tpwrules/emdash/dashboard/src_gen/pic_data.c

#include <inttypes.h>
#include "../src/pic_data.h"

static const uint8_t pic_bytes[3980] = {
113,7,60,72,201,7,27,214,48,31,32,7,56,201,3,27,8,195,1,54,
66,136,194,4,146,195,25,62,3,63,56,201,3,27,24,195,1,2,12,55,
12,38,115,1,38,12,3,8,39,21,35,12,83,56,31,60,24,201,3,25,
24,195,1,50,21,2,17,21,9,6,117,20,6,21,50,28,52,20,79,35,
63,197,15,63,63,194,3,9,24,195,1,2,25,2,17,21,9,3,1,21,
20,3,20,34,29,20,24,94,15,56,195,1,63,63,63,63,63,60,65,45,
40,195,1,55,12,51,16,37,8,54,1,53,12,6,8,35,29,52,12,1,
56,31,32,7,48,191,63,63,63,63,63,63,56,1,45,40,212,3,33,62,
3,63,48,71,48,67,63,63,63,63,63,33,45,40,196,1,129,65,32,65,
80,1,4,132,15,3,56,31,61,48,94,3,63,48,63,63,60,1,63,57,
37,40,196,2,8,48,21,35,12,32,25,35,118,13,38,9,35,12,12,15,
3,63,32,65,56,63,63,62,15,63,51,60,125,36,32,196,7,21,93,21,
20,32,13,21,1,19,25,21,20,52,20,124,15,60,131,33,63,63,63,47,
63,15,63,60,14,52,32,196,2,21,93,22,24,32,21,21,1,21,13,21,
21,20,20,1,48,63,48,31,63,63,9,63,63,63,47,63,31,63,60,55,
54,48,196,2,9,93,19,13,48,29,19,119,25,22,9,52,12,7,3,62,
3,63,63,62,29,63,63,63,47,62,31,63,60,59,54,48,213,15,56,31,
56,63,60,61,63,63,63,47,62,63,63,60,61,54,48,197,4,52,1,35,
9,48,29,194,1,16,8,194,63,3,63,127,61,61,63,63,63,47,62,63,
63,60,61,54,48,197,9,2,85,25,16,9,34,29,35,1,22,28,50,24,
3,56,31,56,127,57,61,63,63,63,47,62,63,63,60,62,54,16,197,9,
2,101,9,48,9,21,28,54,1,51,9,37,20,31,1,63,71,63,59,61,
63,63,63,47,62,63,63,60,62,62,24,197,9,2,1,5,9,16,9,21,
29,19,1,53,8,53,20,24,15,56,1,63,63,51,61,63,63,63,15,62,
31,63,60,62,59,24,197,4,52,1,54,9,48,9,18,21,54,1,23,13,
34,20,1,62,95,49,63,55,60,63,63,63,31,63,31,63,60,62,59,24,
212,15,32,7,62,1,63,39,60,63,63,63,31,63,31,63,60,62,59,24,
195,8,36,1,194,4,32,152,68,68,80,56,1,63,65,63,39,60,63,63,
63,31,63,31,63,60,62,59,195,3,1,54,21,32,12,39,5,54,20,53,
8,51,4,55,13,35,24,95,48,71,63,39,60,63,63,63,31,63,47,63,
60,62,63,195,5,8,37,21,16,17,23,8,37,29,5,9,22,9,23,20,
54,20,3,60,67,63,63,39,60,63,63,62,63,63,47,63,60,62,63,195,
7,8,37,21,16,17,23,16,37,29,5,9,35,17,39,21,19,20,6,191,
49,63,39,62,63,63,62,62,15,47,63,60,62,63,195,1,8,53,13,34,
12,37,16,54,29,3,28,54,16,53,13,54,20,191,60,1,63,39,62,63,
63,62,60,15,55,63,60,62,63,195,2,198,4,201,63,62,65,63,39,62,
63,63,61,56,7,55,63,60,62,61,213,3,48,129,63,55,62,63,63,61,
56,7,59,63,60,60,60,216,3,49,63,51,62,31,63,59,48,7,59,63,
60,61,28,215,1,63,48,123,62,31,63,51,48,3,61,63,60,61,28,213,
3,63,63,60,137,62,31,63,39,32,3,62,63,60,59,28,206,6,203,12,
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

};

const pic_data_t picture_data_records[18] = {
{&pic_bytes[0], 40, 64},
{&pic_bytes[1484], 64, 32},
{&pic_bytes[3044], 4, 15},
{&pic_bytes[3080], 4, 15},
{&pic_bytes[3120], 4, 15},
{&pic_bytes[3162], 4, 15},
{&pic_bytes[3202], 4, 15},
{&pic_bytes[3248], 4, 15},
{&pic_bytes[3300], 4, 15},
{&pic_bytes[3339], 4, 15},
{&pic_bytes[3373], 3, 15},
{&pic_bytes[3399], 3, 15},
{&pic_bytes[3424], 3, 15},
{&pic_bytes[3449], 5, 31},
{&pic_bytes[3588], 5, 31},
{&pic_bytes[3680], 5, 31},
{&pic_bytes[3786], 5, 31},
{&pic_bytes[3887], 5, 31},
};
