tpwrules/emdash/dashboard/src_gen/can_log.c

#include "../src_11c24/can_log.h"

const can_log_entry_t can_log_entries[] = {
{93,289,8,{0,0,112,23,146,198,112,23}},
{93,290,5,{129,90,169,73,11,0,0,0}},
{93,257,3,{62,10,0,0,0,0,0,0}},
{93,274,6,{0,0,0,0,65,0,0,0}},
{93,276,7,{0,0,0,0,0,0,61,0}},
{93,281,8,{0,0,1,0,0,0,0,0}},
{93,305,7,{0,0,0,0,0,0,0,0}},
{98,289,8,{0,0,160,24,146,198,160,24}},
{104,289,8,{0,0,208,25,146,198,208,25}},
{109,289,8,{0,0,255,26,146,198,255,26}},
{116,289,8,{0,0,43,28,146,198,43,28}},
{121,289,8,{0,0,85,29,146,198,85,29}},
{127,289,8,{0,0,122,30,146,198,122,30}},
{132,289,8,{0,0,155,31,146,198,155,31}},
{137,289,8,{0,0,183,32,146,198,183,32}},
{142,289,8,{0,0,205,33,146,198,205,33}},
{148,289,8,{0,0,220,34,146,198,220,34}},
{148,281,8,{0,0,0,0,0,0,0,1}},
{148,257,3,{62,10,1,0,0,0,0,0}},
{153,289,8,{0,0,228,35,146,198,228,35}},
{158,289,8,{0,0,228,36,146,198,228,36}},
{164,289,8,{0,0,219,37,146,198,219,37}},
{169,289,8,{0,0,201,38,146,198,201,38}},
{175,289,8,{0,0,173,39,146,198,173,39}},
{180,289,8,{0,0,135,40,146,198,135,40}},
{185,289,8,{0,0,86,41,146,198,86,41}},
{191,289,8,{0,0,26,42,146,198,26,42}},
{196,289,8,{0,0,209,42,146,198,209,42}},
{202,289,8,{0,0,124,43,146,198,124,43}},
{202,281,8,{0,0,1,0,0,0,0,2}},
{202,257,3,{62,10,0,0,0,0,0,0}},
{207,289,8,{0,0,27,44,146,198,27,44}},
{213,289,8,{0,0,172,44,146,198,172,44}},
{218,289,8,{0,0,47,45,146,198,47,45}},
{223,289,8,{0,0,165,45,146,198,165,45}},
{229,289,8,{0,0,12,46,146,198,12,46}},
{234,289,8,{0,0,101,46,146,198,101,46}},
{240,289,8,{0,0,175,46,146,198,175,46}},
{245,289,8,{0,0,235,46,146,198,224,46}},
{250,289,8,{0,0,23,47,146,198,224,46}},
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
};
