tpwrules/emdash/dashboard/src_gen/pic_ids.h

#ifndef PIC_IDS_H
#define PIC_IDS_H

#define PIC_NUMBER_OF_IDS (18)

#define PIC_ID_BOOTSPLASH (0)
#define PIC_ID_FONT_6X8 (1)
#define PIC_ID_OIL_PRESSURE (2)
#define PIC_ID_OIL_TEMP (3)
#define PIC_ID_WATER_TEMP (4)
#define PIC_ID_BLOCK_TEMP (5)
#define PIC_ID_FUEL_PRESSURE (6)
#define PIC_ID_FUEL_TEMP (7)
#define PIC_ID_BATTERY (8)
#define PIC_ID_OIL_TEMP_LOW (9)
#define PIC_ID_RADIO (10)
#define PIC_ID_UPSHIFT_BTN (11)
#define PIC_ID_DOWNSHIFT_BTN (12)
#define PIC_ID_GEAR_NEUTRAL (13)
#define PIC_ID_GEAR_1 (14)
#define PIC_ID_GEAR_2 (15)
#define PIC_ID_GEAR_3 (16)
#define PIC_ID_GEAR_4 (17)

#endif
