tpwrules/emdash/dashboard/src/pic_data.h

#ifndef PIC_DATA_H
#define PIC_DATA_H

#include "platform.h"
#include "../src_gen/pic_ids.h"

typedef struct {
    const uint8_t *data; // pointer to picture data
    uint8_t width; // in bytes
    uint8_t height; // in pixels
} pic_data_t;


#ifndef PLATFORM_PC
extern const pic_data_t picture_data_records[PIC_NUMBER_OF_IDS];
#endif

#endif
