tpwrules/emdash/boot_pc/pc_programmer.py

# connection information
VECTOR_APP_NAME = "emdash"
VECTOR_CHANNEL = 0
CAN_BAUDRATE = 500000

# bootloader information
BOOTLOAD_CAN_CMD_ADDR = 0x7EF
BOOTLOAD_CAN_RESP_ADDR = 0x7EE

# map from system names to IDs
BOOTLOAD_SYS_NAME_MAP = {
    "dashboard": 1,
    "wheelboard": 2
}

# the same map, from IDs to system names
BOOTLOAD_SYS_ID_MAP = {v: k for k, v in BOOTLOAD_SYS_NAME_MAP.items()}

import argparse
import struct
import binascii
import time

parser = argparse.ArgumentParser(description=
    "Program the Einstein Motorsport dashboard or wheelboard over CAN.")
parser.add_argument('application', type=str, nargs='?',
    help="Application memory image (.bin) to use.")
parser.add_argument('-u', '--utilization', type=int, default=25,
    help="Maximum bus utilization permitted, in percent. Higher values "
         "allow faster programming, but may cause other devices on the "
         "bus to function incorrectly. Integer between 1 and 100, "
         "default value is 25.")
parser.add_argument('-v', '--verbose', action="store_true", default=False,
    help="Provide more detail during programming and after errors.")
parser.add_argument('-d', '--device', type=str, default=None,
    help="Specify the name of the device to program. If not specified, "
         "the ID stored in the header of the application image is used.")

args_tasks = parser.add_argument_group("tasks", 
    "Tasks for programmer to perform. You can select multiple tasks.")
args_tasks.add_argument('-i', '--info', action="store_true", default=False,
    help="Show information (version and destination device) stored in "
         "the application image.")
args_tasks.add_argument('-c', '--check', action="store_true", default=False,
    help="Connect to the device and check its bootloader and application "
         "version.")
args_tasks.add_argument('-p', '--program', action="store_true", default=None,
    help="Connect to the device and program the application image into it. "
         "This is the default unless -i or -c is specified.")

args = parser.parse_args()

class BootloadError(Exception):
    pass

class ArgumentError(BootloadError):
    def __str__(self):
        return "Invalid argument: "+super().__str__()

class ImageError(BootloadError):
    def __str__(self):
        return "Application image is corrupt: "+super().__str__()

class CANError(BootloadError):
    def __str__(self):
        return "CAN bus error: "+super().__str__()

class ProgramError(BootloadError):
    def __str__(self):
        return "Programming failed: "+super().__str__()

import subprocess

def str_version_real(num):
    # stringify number into commit hash
    commit = "{:08x}".format(num)

    def git(*args):
        return subprocess.check_output(("git", *args), timeout=5,
            stderr=subprocess.STDOUT).decode("utf8").strip()

    # ask git for the full tag name (i.e. the tag name and the next commit)
    full_tag_name = git("describe", commit)
    # plus the base tag name
    tag_name = git("describe", "--abbrev=0", commit)
    # now ask for that tag's description
    tag_desc = git("tag", "-n1", tag_name)
    # remove tag name from description
    if tag_desc.startswith(tag_name):
        tag_desc = tag_desc.replace(tag_name, "", 1).strip()
    
    # now get the description of the commit itself
    commit_desc = git("log", "-1", "--format=%s", commit)

    # and finally format everything
    return "{}: {} ({} {})".format(full_tag_name, tag_desc, commit, commit_desc)

def str_version(num):
    # return a string corresponding to the version given
    try:
        return str_version_real(num)
    except:
        return "{:08x} (further information could not be retrieved)".format(num)

def str_build_date(num):
    # return a string corresponding to the build date given
    # for now it's just gross string parsing
    s = str(num)
    return "20"+s[0:2]+"-"+s[2:4]+"-"+s[4:6]+" "+s[6:8]+":"+s[8:10]

def read_image(show_info):
    try:
        imf = open(args.application, "rb")
        image = imf.read()
        imf.close()
    except IOError as e:
        raise ArgumentError("could not read application image: {}".format(
            str(e)))

    # header is 32 bytes
    if len(image) < 32:
        raise ImageError("header is missing.")

    # note that the bootloader does the same tests and checksums
    # so if it passes these, it will pass in the bootloader

    # validate the header checksum
    header = struct.unpack("<8I", image[:32])
    if sum(header) & 0xFFFFFFFF != 0:
        raise ImageError("header checksum failed.")

    # get the header size and crc, then validate it that way
    app_crc = header[4]
    app_size = header[5]
    if app_size < 48*4 or app_size > 0x7000:
        raise ImageError("application size in header is invalid.")
    if app_size != len(image):
        raise ImageError(
            "application size in header doesn't match image size.")

    crc = binascii.crc32(image[32:], 0)
    if crc != app_crc:
        raise ImageError("application checksum failed.")

    # pad the image with 0xFF to be a multiple of 256 bytes
    # (because the image is sent in 256 byte pages)
    if len(image) % 256 != 0:
        image += b"\xFF"*(256-(len(image)%256))

    # get more of the vector table for more information
    header = struct.unpack("<12I", image[:48])

    if show_info:
        print("APPLICATION IMAGE INFORMATION:")
        print("    Device: {} ({})".format(header[8],
            BOOTLOAD_SYS_ID_MAP.get(header[8], "<unknown>")))
        print("    Version:", str_version(header[9]))
        print("    Build date:", str_build_date(header[10]))

    # finally, return the validated and padded image
    # plus the device the image is for
    return image, header[8]

import logging
# importing can prints out some garbage on startup that we don't want to see
# so we shut it up until import is finished
logging.disable(logging.CRITICAL)
import can
logging.disable(logging.NOTSET)

CMD_HELLO = 0
CMD_ERASE_ALL = 1
CMD_EMPTY = 2
CMD_PROGRAM_VERIFY = 3
CMD_REBOOT = 4
CMD_READ_FLASH = 5

RESP_SUCCESS = 0
RESP_HELLO = 1
RESP_INVALID_COMMAND = 2
RESP_ERROR = 3
RESP_PROGRAM_FAILURE = 4
RESP_CHECKSUM_INCORRECT = 5

CMD_HELLO_KEY = 0xb00710ad

class CAN:
    def __init__(self, app_name, channel, baudrate, utilization):
        try:
            self.bus = can.interface.Bus(
                bustype='vector',
                app_name=app_name,
                channel=channel,
                bitrate=baudrate,
                receive_own_messages=True
            )
        except can.interfaces.vector.exceptions.VectorError as e:
            msg = str(e)
            if "xlGetApplConfig" in msg or "XL_ERROR" in msg:
                raise CANError("could not initialize. "
                    "Is the Vector Hardware application configuration correct?") from e
            elif "XL_ERR_WRONG_PARAMETER" in msg or \
                    "XL_ERR_HW_NOT_PRESENT" in msg: # how i want it to be reported
                raise CANError("could not initialize. "
                    "Is the interface plugged in?") from e
            else:
                raise CANError("could not initialize: "+str(e)) from e
        except ValueError as e:
            # thrown by python-can 2.2.0 in this case
            # may be hiding something else but idk what to do
            raise CANError("could not initialize. "
                "Is the interface plugged in?") from e
        except Exception as e:
            raise CANError("could not initialize: "+str(e)) from e

        # calculate message interval allowed by the utilization factor
        # a CAN message can be at most 132 bits long, assuming DLC of 8
        # and worst-case stuffing
        msgs_per_sec = (baudrate/132) * (utilization/100)
        self.msg_interval = 1/msgs_per_sec

        self.last_cmd = None
        self.msgs_sent = 0
        self.next_msg_time = time.perf_counter()

    def recv_filtered(self, timeout):
        # apparently can_filters just doesn't work
        # so we'll have to do it ourselves!
        while timeout > 0:
            start = time.monotonic()
            m = self.bus.recv(timeout)
            # subtract time elapsed from timeout duration
            # in case we need to recv again
            timeout -= time.monotonic()-start
            # but if m is None, we've timed out for real
            if m is None:
                return None

            if (m.arbitration_id == BOOTLOAD_CAN_CMD_ADDR or
                    m.arbitration_id == BOOTLOAD_CAN_RESP_ADDR) and \
                    m.is_error_frame is False:
                # a message made it past the filter
                return m
        # we've timed out also if timeout <= 0
        return None

    def send_data(self, data):
        self.last_cmd = data[0] # used to verify response
        m = can.Message(arbitration_id=BOOTLOAD_CAN_CMD_ADDR,
            data=data, extended_id=False)
        self.msgs_sent += 1

        # busywait until we're allowed to send the next message
        # sleeping is way too slow
        now = time.perf_counter()
        while self.next_msg_time > now:
            time.sleep(0)
            now = time.perf_counter()
        self.bus.send(m)
        self.bus.flush_tx_buffer()
        # allow next message to be sent at the interval
        # calculated to allow the desired bus utilizaton
        self.next_msg_time = now + self.msg_interval

        # next received message should be the transmission receipt
        m = self.recv_filtered(timeout=5)
        if m is None:
            raise CANError("timed out waiting for message to be transmitted. "
                "Are CANH and CANL connected properly?")
        if m.arbitration_id != BOOTLOAD_CAN_CMD_ADDR or m.data != data:
            raise CANError("received message unexpectedly: "+str(m))

    def recv_response(self, timeout=5, expected_resp=None):
        m = self.recv_filtered(timeout=timeout)
        if m is None:
            raise CANError("timed out waiting for message to be received.")
        if len(m.data) != 6:
            raise ProgramError("response length is incorrect: {}".format(len(m.data)))
        cmd, resp, data = struct.unpack("<BBI", m.data)
        # some responses we can deal with here
        if cmd != self.last_cmd:
            raise ProgramError("received response to incorrect command: {}".format(cmd))
        elif cmd > CMD_READ_FLASH:
            raise ProgramError("received response for invalid command: {}".format(cmd))
        if resp == RESP_INVALID_COMMAND:
            raise ProgramError("received 'invalid command' response.")
        elif resp == RESP_ERROR:
            raise ProgramError("unexpected error inside bootloader.")
        elif resp == RESP_PROGRAM_FAILURE:
            raise ProgramError("Flash programming failure. Chip may be damaged.")
        elif expected_resp is not None and resp != expected_resp:
            raise ProgramError("unexpected response: {}".format(cmd))
        # otherwise, return it for the caller
        return resp, data


class Programmer:
    def __init__(self, bus):
        self.bus = bus

    def connect(self, device):
        # try to send the Hello command until we get a response
        while True:
            self.bus.send_data(struct.pack("<BHI",
                CMD_HELLO, device, CMD_HELLO_KEY))
            try:
                resp, data = self.bus.recv_response(
                    timeout=0.1, expected_resp=RESP_HELLO)
                break
            except CANError:
                continue
        # data is nonzero if application is valid
        return True if data else False

    def erase(self):
        # send erase command and wait for it to happen
        self.bus.send_data(struct.pack("<B", CMD_ERASE_ALL))
        self.bus.recv_response(expected_resp=RESP_SUCCESS)

    def program_page(self, page, pdata):
        # try multiple times in case data transfer failed
        for program_try in range(5):
            # empty page buffer
            self.bus.send_data(struct.pack("<B", CMD_EMPTY))
            self.bus.recv_response(expected_resp=RESP_SUCCESS)

            # send the page in 8 byte chunks
            for pos in range(0, 256, 8):
                self.bus.send_data(pdata[pos:pos+8])

            # checksum the page
            crc = binascii.crc32(pdata, 0)
            # and now program it
            self.bus.send_data(struct.pack("<BHI", CMD_PROGRAM_VERIFY,
                page, crc))
            resp, data = self.bus.recv_response()
            if resp == RESP_CHECKSUM_INCORRECT:
                continue
            if resp == RESP_SUCCESS:
                break
            raise ProgramError("unexpected response: {}".format(resp))
        else: # loop did not break -> we were never successful
            raise ProgramError("page transfer failed 5 times. "
                "Are CANH and CANL connected properly? Is there noise on the bus?")

    def reboot(self):
        # send reboot command and wait for it to happen
        # True tells bootloader to reboot into app
        self.bus.send_data(struct.pack("<BB", CMD_REBOOT, True))
        self.bus.recv_response(expected_resp=RESP_SUCCESS)

    def read_flash(self, addr):
        # send read flash command
        self.bus.send_data(struct.pack("<BI", CMD_READ_FLASH, addr))
        # wait for data to come back
        resp, data = self.bus.recv_response(expected_resp=RESP_SUCCESS)
        return data


def main():
    # enforce argument logic
    # make sure program is default
    if args.program is None:
        if args.info or args.check:
            args.program = False
        else:
            args.program = True
    # make sure an app image is specified if required
    if args.application is None:
        if args.info:
            raise ArgumentError("application image required to check "
                                "application image information.")
        if args.program:
            raise ArgumentError("application image required to program.")
        if args.check and args.device is None:
            raise ArgumentError("provide application image or use -d to select "
                                "device to check.")
    # figure out what device the user wants
    device = None
    if args.device is not None:
        device = BOOTLOAD_SYS_NAME_MAP.get(args.device.strip().lower())
        if device is None:
            raise ArgumentError("unrecognized device: '{}'".format(args.device))
    # check that utilization is within range
    if args.utilization < 1 or args.utilization > 100:
        raise ArgumentError(
            "utilization percent must be an integer between 1 and 100.")

    # read in the image data if necessary
    # also display info about it, if asked
    if args.info or args.program or device is None:
        image, app_device = read_image(args.info)
        if not args.program and not args.check:
            return # info is all we need to do. program finished
        if device is None:
            device = app_device
        elif device != app_device:
            raise ImageError("application image does not match requested device.")

    # now that is done, initialize the CAN interface
    bus = CAN(VECTOR_APP_NAME,
        VECTOR_CHANNEL,
        CAN_BAUDRATE,
        args.utilization)

    # now we can do the programming! make a programmer
    prog = Programmer(bus)

    # and run through all the steps
    print("Connecting to device... ", end="", flush=True)
    app_valid = prog.connect(device)
    print("connected!")

    # print out the check information if asked
    if args.check:
        print("DEVICE CHECK INFORMATION:")
        print("    Bootloader version:", str_version(prog.read_flash(4*9)))
        print("    Bootloader build date:", str_build_date(prog.read_flash(4*10)))
        print("    Application is valid: {}".format(app_valid))
        if app_valid:
            print("    Application version:", 
                str_version(prog.read_flash(0x1000+(4*9))))
            print("    Application build date:",
                str_build_date(prog.read_flash(0x1000+(4*10))))

    if args.program:
        print("Erasing Flash... ", end="", flush=True)
        prog.erase()
        print("erased!")

        num_pages = int(len(image)/256)
        for page in range(num_pages):
            print("\rProgramming page {}/{}... ".format(page+1, num_pages),
                end="", flush=True)
            prog.program_page(page, image[page*256:page*256+256])
        print("programmed!")

    print("Rebooting into application... ", end="", flush=True)
    prog.reboot()
    print("rebooted!")
    print("")
    print("Task Complete")

if args.verbose:
    main()
else:
    try:
        main()
    except KeyboardInterrupt:
        print("\nCancelled.")
    except BootloadError as e:
        print(str(e))
        exit(1)
